daveshah1/openMixR/fpga/vivado/openmixr_base/openmixr_base.cache/ip/b018d6374f05f04f/init_config_rom_stub.v

// Copyright 1986-2016 Xilinx, Inc. All Rights Reserved.
// --------------------------------------------------------------------------------
// Tool Version: Vivado v.2016.3 (lin64) Build 1682563 Mon Oct 10 19:07:26 MDT 2016
// Date        : Thu May  4 16:19:46 2017
// Host        : david-desktop-arch running 64-bit unknown
// Command     : write_verilog -force -mode synth_stub -rename_top decalper_eb_ot_sdeen_pot_pi_dehcac_xnilix -prefix
//               decalper_eb_ot_sdeen_pot_pi_dehcac_xnilix_ init_config_rom_stub.v
// Design      : init_config_rom
// Purpose     : Stub declaration of top-level module interface
// Device      : xc7a200tfbg484-3
// --------------------------------------------------------------------------------

// This empty module with port declaration file causes synthesis tools to infer a black box for IP.
// The synthesis directives are for Synopsys Synplify support to prevent IO buffer insertion.
// Please paste the declaration into a Verilog source file or add the file as an additional source.
(* x_core_info = "blk_mem_gen_v8_3_4,Vivado 2016.3" *)
module decalper_eb_ot_sdeen_pot_pi_dehcac_xnilix(clka, addra, douta)
/* synthesis syn_black_box black_box_pad_pin="clka,addra[9:0],douta[31:0]" */;
  input clka;
  input [9:0]addra;
  output [31:0]douta;
endmodule
