daveshah1/openMixR/fpga/vivado/openmixr_base/openmixr_base.cache/ip/b018d6374f05f04f/init_config_rom_sim_netlist.v

// Copyright 1986-2016 Xilinx, Inc. All Rights Reserved.
// --------------------------------------------------------------------------------
// Tool Version: Vivado v.2016.3 (lin64) Build 1682563 Mon Oct 10 19:07:26 MDT 2016
// Date        : Thu May  4 16:19:46 2017
// Host        : david-desktop-arch running 64-bit unknown
// Command     : write_verilog -force -mode funcsim -rename_top decalper_eb_ot_sdeen_pot_pi_dehcac_xnilix -prefix
//               decalper_eb_ot_sdeen_pot_pi_dehcac_xnilix_ init_config_rom_sim_netlist.v
// Design      : init_config_rom
// Purpose     : This verilog netlist is a functional simulation representation of the design and should not be modified
//               or synthesized. This netlist cannot be used for SDF annotated simulation.
// Device      : xc7a200tfbg484-3
// --------------------------------------------------------------------------------
`timescale 1 ps / 1 ps

(* CHECK_LICENSE_TYPE = "init_config_rom,blk_mem_gen_v8_3_4,{}" *) (* downgradeipidentifiedwarnings = "yes" *) (* x_core_info = "blk_mem_gen_v8_3_4,Vivado 2016.3" *) 
(* NotValidForBitStream *)
module decalper_eb_ot_sdeen_pot_pi_dehcac_xnilix
   (clka,
    addra,
    douta);
  (* x_interface_info = "xilinx.com:interface:bram:1.0 BRAM_PORTA CLK" *) input clka;
  (* x_interface_info = "xilinx.com:interface:bram:1.0 BRAM_PORTA ADDR" *) input [9:0]addra;
  (* x_interface_info = "xilinx.com:interface:bram:1.0 BRAM_PORTA DOUT" *) output [31:0]douta;

  wire [9:0]addra;
  wire clka;
  wire [31:0]douta;
  wire NLW_U0_dbiterr_UNCONNECTED;
  wire NLW_U0_rsta_busy_UNCONNECTED;
  wire NLW_U0_rstb_busy_UNCONNECTED;
  wire NLW_U0_s_axi_arready_UNCONNECTED;
  wire NLW_U0_s_axi_awready_UNCONNECTED;
  wire NLW_U0_s_axi_bvalid_UNCONNECTED;
  wire NLW_U0_s_axi_dbiterr_UNCONNECTED;
  wire NLW_U0_s_axi_rlast_UNCONNECTED;
  wire NLW_U0_s_axi_rvalid_UNCONNECTED;
  wire NLW_U0_s_axi_sbiterr_UNCONNECTED;
  wire NLW_U0_s_axi_wready_UNCONNECTED;
  wire NLW_U0_sbiterr_UNCONNECTED;
  wire [31:0]NLW_U0_doutb_UNCONNECTED;
  wire [9:0]NLW_U0_rdaddrecc_UNCONNECTED;
  wire [3:0]NLW_U0_s_axi_bid_UNCONNECTED;
  wire [1:0]NLW_U0_s_axi_bresp_UNCONNECTED;
  wire [9:0]NLW_U0_s_axi_rdaddrecc_UNCONNECTED;
  wire [31:0]NLW_U0_s_axi_rdata_UNCONNECTED;
  wire [3:0]NLW_U0_s_axi_rid_UNCONNECTED;
  wire [1:0]NLW_U0_s_axi_rresp_UNCONNECTED;

  (* C_ADDRA_WIDTH = "10" *) 
  (* C_ADDRB_WIDTH = "10" *) 
  (* C_ALGORITHM = "1" *) 
  (* C_AXI_ID_WIDTH = "4" *) 
  (* C_AXI_SLAVE_TYPE = "0" *) 
  (* C_AXI_TYPE = "1" *) 
  (* C_BYTE_SIZE = "9" *) 
  (* C_COMMON_CLK = "0" *) 
  (* C_COUNT_18K_BRAM = "0" *) 
  (* C_COUNT_36K_BRAM = "1" *) 
  (* C_CTRL_ECC_ALGO = "NONE" *) 
  (* C_DEFAULT_DATA = "0" *) 
  (* C_DISABLE_WARN_BHV_COLL = "0" *) 
  (* C_DISABLE_WARN_BHV_RANGE = "0" *) 
  (* C_ELABORATION_DIR = "./" *) 
  (* C_ENABLE_32BIT_ADDRESS = "0" *) 
  (* C_EN_DEEPSLEEP_PIN = "0" *) 
  (* C_EN_ECC_PIPE = "0" *) 
  (* C_EN_RDADDRA_CHG = "0" *) 
  (* C_EN_RDADDRB_CHG = "0" *) 
  (* C_EN_SAFETY_CKT = "0" *) 
  (* C_EN_SHUTDOWN_PIN = "0" *) 
  (* C_EN_SLEEP_PIN = "0" *) 
  (* C_EST_POWER_SUMMARY = "Estimated Power for IP     :     2.622 mW" *) 
  (* C_FAMILY = "artix7" *) 
  (* C_HAS_AXI_ID = "0" *) 
  (* C_HAS_ENA = "0" *) 
  (* C_HAS_ENB = "0" *) 
  (* C_HAS_INJECTERR = "0" *) 
  (* C_HAS_MEM_OUTPUT_REGS_A = "0" *) 
  (* C_HAS_MEM_OUTPUT_REGS_B = "0" *) 
  (* C_HAS_MUX_OUTPUT_REGS_A = "0" *) 
  (* C_HAS_MUX_OUTPUT_REGS_B = "0" *) 
  (* C_HAS_REGCEA = "0" *) 
  (* C_HAS_REGCEB = "0" *) 
  (* C_HAS_RSTA = "0" *) 
  (* C_HAS_RSTB = "0" *) 
  (* C_HAS_SOFTECC_INPUT_REGS_A = "0" *) 
  (* C_HAS_SOFTECC_OUTPUT_REGS_B = "0" *) 
  (* C_INITA_VAL = "0" *) 
  (* C_INITB_VAL = "0" *) 
  (* C_INIT_FILE = "init_config_rom.mem" *) 
  (* C_INIT_FILE_NAME = "no_coe_file_loaded" *) 
  (* C_INTERFACE_TYPE = "0" *) 
  (* C_LOAD_INIT_FILE = "0" *) 
  (* C_MEM_TYPE = "3" *) 
  (* C_MUX_PIPELINE_STAGES = "0" *) 
  (* C_PRIM_TYPE = "1" *) 
  (* C_READ_DEPTH_A = "1024" *) 
  (* C_READ_DEPTH_B = "1024" *) 
  (* C_READ_WIDTH_A = "32" *) 
  (* C_READ_WIDTH_B = "32" *) 
  (* C_RSTRAM_A = "0" *) 
  (* C_RSTRAM_B = "0" *) 
  (* C_RST_PRIORITY_A = "CE" *) 
  (* C_RST_PRIORITY_B = "CE" *) 
  (* C_SIM_COLLISION_CHECK = "ALL" *) 
  (* C_USE_BRAM_BLOCK = "0" *) 
  (* C_USE_BYTE_WEA = "0" *) 
  (* C_USE_BYTE_WEB = "0" *) 
  (* C_USE_DEFAULT_DATA = "0" *) 
  (* C_USE_ECC = "0" *) 
  (* C_USE_SOFTECC = "0" *) 
  (* C_USE_URAM = "0" *) 
  (* C_WEA_WIDTH = "1" *) 
  (* C_WEB_WIDTH = "1" *) 
  (* C_WRITE_DEPTH_A = "1024" *) 
  (* C_WRITE_DEPTH_B = "1024" *) 
  (* C_WRITE_MODE_A = "WRITE_FIRST" *) 
  (* C_WRITE_MODE_B = "WRITE_FIRST" *) 
  (* C_WRITE_WIDTH_A = "32" *) 
  (* C_WRITE_WIDTH_B = "32" *) 
  (* C_XDEVICEFAMILY = "artix7" *) 
  (* downgradeipidentifiedwarnings = "yes" *) 
  decalper_eb_ot_sdeen_pot_pi_dehcac_xnilix_blk_mem_gen_v8_3_4 U0
       (.addra(addra),
        .addrb({1'b0,1'b0,1'b0,1'b0,1'b0,1'b0,1'b0,1'b0,1'b0,1'b0}),
        .clka(clka),
        .clkb(1'b0),
        .dbiterr(NLW_U0_dbiterr_UNCONNECTED),
        .deepsleep(1'b0),
        .dina({1'b0,1'b0,1'b0,1'b0,1'b0,1'b0,1'b0,1'b0,1'b0,1'b0,1'b0,1'b0,1'b0,1'b0,1'b0,1'b0,1'b0,1'b0,1'b0,1'b0,1'b0,1'b0,1'b0,1'b0,1'b0,1'b0,1'b0,1'b0,1'b0,1'b0,1'b0,1'b0}),
        .dinb({1'b0,1'b0,1'b0,1'b0,1'b0,1'b0,1'b0,1'b0,1'b0,1'b0,1'b0,1'b0,1'b0,1'b0,1'b0,1'b0,1'b0,1'b0,1'b0,1'b0,1'b0,1'b0,1'b0,1'b0,1'b0,1'b0,1'b0,1'b0,1'b0,1'b0,1'b0,1'b0}),
        .douta(douta),
        .doutb(NLW_U0_doutb_UNCONNECTED[31:0]),
        .eccpipece(1'b0),
        .ena(1'b0),
        .enb(1'b0),
        .injectdbiterr(1'b0),
        .injectsbiterr(1'b0),
        .rdaddrecc(NLW_U0_rdaddrecc_UNCONNECTED[9:0]),
        .regcea(1'b0),
        .regceb(1'b0),
        .rsta(1'b0),
        .rsta_busy(NLW_U0_rsta_busy_UNCONNECTED),
        .rstb(1'b0),
        .rstb_busy(NLW_U0_rstb_busy_UNCONNECTED),
        .s_aclk(1'b0),
        .s_aresetn(1'b0),
        .s_axi_araddr({1'b0,1'b0,1'b0,1'b0,1'b0,1'b0,1'b0,1'b0,1'b0,1'b0,1'b0,1'b0,1'b0,1'b0,1'b0,1'b0,1'b0,1'b0,1'b0,1'b0,1'b0,1'b0,1'b0,1'b0,1'b0,1'b0,1'b0,1'b0,1'b0,1'b0,1'b0,1'b0}),
        .s_axi_arburst({1'b0,1'b0}),
        .s_axi_arid({1'b0,1'b0,1'b0,1'b0}),
        .s_axi_arlen({1'b0,1'b0,1'b0,1'b0,1'b0,1'b0,1'b0,1'b0}),
        .s_axi_arready(NLW_U0_s_axi_arready_UNCONNECTED),
        .s_axi_arsize({1'b0,1'b0,1'b0}),
        .s_axi_arvalid(1'b0),
        .s_axi_awaddr({1'b0,1'b0,1'b0,1'b0,1'b0,1'b0,1'b0,1'b0,1'b0,1'b0,1'b0,1'b0,1'b0,1'b0,1'b0,1'b0,1'b0,1'b0,1'b0,1'b0,1'b0,1'b0,1'b0,1'b0,1'b0,1'b0,1'b0,1'b0,1'b0,1'b0,1'b0,1'b0}),
        .s_axi_awburst({1'b0,1'b0}),
        .s_axi_awid({1'b0,1'b0,1'b0,1'b0}),
        .s_axi_awlen({1'b0,1'b0,1'b0,1'b0,1'b0,1'b0,1'b0,1'b0}),
        .s_axi_awready(NLW_U0_s_axi_awready_UNCONNECTED),
        .s_axi_awsize({1'b0,1'b0,1'b0}),
        .s_axi_awvalid(1'b0),
        .s_axi_bid(NLW_U0_s_axi_bid_UNCONNECTED[3:0]),
        .s_axi_bready(1'b0),
        .s_axi_bresp(NLW_U0_s_axi_bresp_UNCONNECTED[1:0]),
        .s_axi_bvalid(NLW_U0_s_axi_bvalid_UNCONNECTED),
        .s_axi_dbiterr(NLW_U0_s_axi_dbiterr_UNCONNECTED),
        .s_axi_injectdbiterr(1'b0),
        .s_axi_injectsbiterr(1'b0),
        .s_axi_rdaddrecc(NLW_U0_s_axi_rdaddrecc_UNCONNECTED[9:0]),
        .s_axi_rdata(NLW_U0_s_axi_rdata_UNCONNECTED[31:0]),
        .s_axi_rid(NLW_U0_s_axi_rid_UNCONNECTED[3:0]),
        .s_axi_rlast(NLW_U0_s_axi_rlast_UNCONNECTED),
        .s_axi_rready(1'b0),
        .s_axi_rresp(NLW_U0_s_axi_rresp_UNCONNECTED[1:0]),
        .s_axi_rvalid(NLW_U0_s_axi_rvalid_UNCONNECTED),
        .s_axi_sbiterr(NLW_U0_s_axi_sbiterr_UNCONNECTED),
        .s_axi_wdata({1'b0,1'b0,1'b0,1'b0,1'b0,1'b0,1'b0,1'b0,1'b0,1'b0,1'b0,1'b0,1'b0,1'b0,1'b0,1'b0,1'b0,1'b0,1'b0,1'b0,1'b0,1'b0,1'b0,1'b0,1'b0,1'b0,1'b0,1'b0,1'b0,1'b0,1'b0,1'b0}),
        .s_axi_wlast(1'b0),
        .s_axi_wready(NLW_U0_s_axi_wready_UNCONNECTED),
        .s_axi_wstrb(1'b0),
        .s_axi_wvalid(1'b0),
        .sbiterr(NLW_U0_sbiterr_UNCONNECTED),
        .shutdown(1'b0),
        .sleep(1'b0),
        .wea(1'b0),
        .web(1'b0));
endmodule

module decalper_eb_ot_sdeen_pot_pi_dehcac_xnilix_blk_mem_gen_generic_cstr
   (douta,
    clka,
    addra);
  output [31:0]douta;
  input clka;
  input [9:0]addra;

  wire [9:0]addra;
  wire clka;
  wire [31:0]douta;

  decalper_eb_ot_sdeen_pot_pi_dehcac_xnilix_blk_mem_gen_prim_width \ramloop[0].ram.r 
       (.addra(addra),
        .clka(clka),
        .douta(douta));
endmodule

module decalper_eb_ot_sdeen_pot_pi_dehcac_xnilix_blk_mem_gen_prim_width
   (douta,
    clka,
    addra);
  output [31:0]douta;
  input clka;
  input [9:0]addra;

  wire [9:0]addra;
  wire clka;
  wire [31:0]douta;

  decalper_eb_ot_sdeen_pot_pi_dehcac_xnilix_blk_mem_gen_prim_wrapper \prim_noinit.ram 
       (.addra(addra),
        .clka(clka),
        .douta(douta));
endmodule

module decalper_eb_ot_sdeen_pot_pi_dehcac_xnilix_blk_mem_gen_prim_wrapper
   (douta,
    clka,
    addra);
  output [31:0]douta;
  input clka;
  input [9:0]addra;

  wire \DEVICE_7SERIES.NO_BMM_INFO.SP.SIMPLE_PRIM36.ram_n_85 ;
  wire \DEVICE_7SERIES.NO_BMM_INFO.SP.SIMPLE_PRIM36.ram_n_86 ;
  wire \DEVICE_7SERIES.NO_BMM_INFO.SP.SIMPLE_PRIM36.ram_n_87 ;
  wire \DEVICE_7SERIES.NO_BMM_INFO.SP.SIMPLE_PRIM36.ram_n_88 ;
  wire [9:0]addra;
  wire clka;
  wire [31:0]douta;
  wire \NLW_DEVICE_7SERIES.NO_BMM_INFO.SP.SIMPLE_PRIM36.ram_CASCADEOUTA_UNCONNECTED ;
  wire \NLW_DEVICE_7SERIES.NO_BMM_INFO.SP.SIMPLE_PRIM36.ram_CASCADEOUTB_UNCONNECTED ;
  wire \NLW_DEVICE_7SERIES.NO_BMM_INFO.SP.SIMPLE_PRIM36.ram_DBITERR_UNCONNECTED ;
  wire \NLW_DEVICE_7SERIES.NO_BMM_INFO.SP.SIMPLE_PRIM36.ram_SBITERR_UNCONNECTED ;
  wire [31:0]\NLW_DEVICE_7SERIES.NO_BMM_INFO.SP.SIMPLE_PRIM36.ram_DOBDO_UNCONNECTED ;
  wire [3:0]\NLW_DEVICE_7SERIES.NO_BMM_INFO.SP.SIMPLE_PRIM36.ram_DOPBDOP_UNCONNECTED ;
  wire [7:0]\NLW_DEVICE_7SERIES.NO_BMM_INFO.SP.SIMPLE_PRIM36.ram_ECCPARITY_UNCONNECTED ;
  wire [8:0]\NLW_DEVICE_7SERIES.NO_BMM_INFO.SP.SIMPLE_PRIM36.ram_RDADDRECC_UNCONNECTED ;

  (* CLOCK_DOMAINS = "COMMON" *) 
  (* box_type = "PRIMITIVE" *) 
  RAMB36E1 #(
    .DOA_REG(0),
    .DOB_REG(0),
    .EN_ECC_READ("FALSE"),
    .EN_ECC_WRITE("FALSE"),
    .INITP_00(256'h0000000000000000000000000000000000000000000000000000000000000000),
    .INITP_01(256'h0000000000000000000000000000000000000000000000000000000000000000),
    .INITP_02(256'h0000000000000000000000000000000000000000000000000000000000000000),
    .INITP_03(256'h0000000000000000000000000000000000000000000000000000000000000000),
    .INITP_04(256'h0000000000000000000000000000000000000000000000000000000000000000),
    .INITP_05(256'h0000000000000000000000000000000000000000000000000000000000000000),
    .INITP_06(256'h0000000000000000000000000000000000000000000000000000000000000000),
    .INITP_07(256'h0000000000000000000000000000000000000000000000000000000000000000),
    .INITP_08(256'h0000000000000000000000000000000000000000000000000000000000000000),
    .INITP_09(256'h0000000000000000000000000000000000000000000000000000000000000000),
    .INITP_0A(256'h0000000000000000000000000000000000000000000000000000000000000000),
    .INITP_0B(256'h0000000000000000000000000000000000000000000000000000000000000000),
    .INITP_0C(256'h0000000000000000000000000000000000000000000000000000000000000000),
    .INITP_0D(256'h0000000000000000000000000000000000000000000000000000000000000000),
    .INITP_0E(256'h0000000000000000000000000000000000000000000000000000000000000000),
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
    .INIT_77(256'h0000000000000000000000000000000000000000000000000000000000000000),
    .INIT_78(256'h0000000000000000000000000000000000000000000000000000000000000000),
    .INIT_79(256'h0000000000000000000000000000000000000000000000000000000000000000),
    .INIT_7A(256'h0000000000000000000000000000000000000000000000000000000000000000),
    .INIT_7B(256'h0000000000000000000000000000000000000000000000000000000000000000),
    .INIT_7C(256'h0000000000000000000000000000000000000000000000000000000000000000),
    .INIT_7D(256'h0000000000000000000000000000000000000000000000000000000000000000),
    .INIT_7E(256'h0000000000000000000000000000000000000000000000000000000000000000),
    .INIT_7F(256'h0000000000000000000000000000000000000000000000000000000000000000),
    .INIT_A(36'h000000000),
    .INIT_B(36'h000000000),
    .INIT_FILE("NONE"),
    .IS_CLKARDCLK_INVERTED(1'b0),
    .IS_CLKBWRCLK_INVERTED(1'b0),
    .IS_ENARDEN_INVERTED(1'b0),
    .IS_ENBWREN_INVERTED(1'b0),
    .IS_RSTRAMARSTRAM_INVERTED(1'b0),
    .IS_RSTRAMB_INVERTED(1'b0),
    .IS_RSTREGARSTREG_INVERTED(1'b0),
    .IS_RSTREGB_INVERTED(1'b0),
    .RAM_EXTENSION_A("NONE"),
    .RAM_EXTENSION_B("NONE"),
    .RAM_MODE("TDP"),
    .RDADDR_COLLISION_HWCONFIG("PERFORMANCE"),
    .READ_WIDTH_A(36),
    .READ_WIDTH_B(36),
    .RSTREG_PRIORITY_A("REGCE"),
    .RSTREG_PRIORITY_B("REGCE"),
    .SIM_COLLISION_CHECK("ALL"),
    .SIM_DEVICE("7SERIES"),
    .SRVAL_A(36'h000000000),
    .SRVAL_B(36'h000000000),
    .WRITE_MODE_A("WRITE_FIRST"),
    .WRITE_MODE_B("WRITE_FIRST"),
    .WRITE_WIDTH_A(36),
    .WRITE_WIDTH_B(36)) 
    \DEVICE_7SERIES.NO_BMM_INFO.SP.SIMPLE_PRIM36.ram 
       (.ADDRARDADDR({1'b1,addra,1'b1,1'b1,1'b1,1'b1,1'b1}),
        .ADDRBWRADDR({1'b0,1'b0,1'b0,1'b0,1'b0,1'b0,1'b0,1'b0,1'b0,1'b0,1'b0,1'b0,1'b0,1'b0,1'b0,1'b0}),
        .CASCADEINA(1'b0),
        .CASCADEINB(1'b0),
        .CASCADEOUTA(\NLW_DEVICE_7SERIES.NO_BMM_INFO.SP.SIMPLE_PRIM36.ram_CASCADEOUTA_UNCONNECTED ),
        .CASCADEOUTB(\NLW_DEVICE_7SERIES.NO_BMM_INFO.SP.SIMPLE_PRIM36.ram_CASCADEOUTB_UNCONNECTED ),
        .CLKARDCLK(clka),
        .CLKBWRCLK(clka),
        .DBITERR(\NLW_DEVICE_7SERIES.NO_BMM_INFO.SP.SIMPLE_PRIM36.ram_DBITERR_UNCONNECTED ),
        .DIADI({1'b0,1'b0,1'b0,1'b0,1'b0,1'b0,1'b0,1'b0,1'b0,1'b0,1'b0,1'b0,1'b0,1'b0,1'b0,1'b0,1'b0,1'b0,1'b0,1'b0,1'b0,1'b0,1'b0,1'b0,1'b0,1'b0,1'b0,1'b0,1'b0,1'b0,1'b0,1'b0}),
        .DIBDI({1'b0,1'b0,1'b0,1'b0,1'b0,1'b0,1'b0,1'b0,1'b0,1'b0,1'b0,1'b0,1'b0,1'b0,1'b0,1'b0,1'b0,1'b0,1'b0,1'b0,1'b0,1'b0,1'b0,1'b0,1'b0,1'b0,1'b0,1'b0,1'b0,1'b0,1'b0,1'b0}),
        .DIPADIP({1'b0,1'b0,1'b0,1'b0}),
        .DIPBDIP({1'b0,1'b0,1'b0,1'b0}),
        .DOADO(douta),
        .DOBDO(\NLW_DEVICE_7SERIES.NO_BMM_INFO.SP.SIMPLE_PRIM36.ram_DOBDO_UNCONNECTED [31:0]),
        .DOPADOP({\DEVICE_7SERIES.NO_BMM_INFO.SP.SIMPLE_PRIM36.ram_n_85 ,\DEVICE_7SERIES.NO_BMM_INFO.SP.SIMPLE_PRIM36.ram_n_86 ,\DEVICE_7SERIES.NO_BMM_INFO.SP.SIMPLE_PRIM36.ram_n_87 ,\DEVICE_7SERIES.NO_BMM_INFO.SP.SIMPLE_PRIM36.ram_n_88 }),
        .DOPBDOP(\NLW_DEVICE_7SERIES.NO_BMM_INFO.SP.SIMPLE_PRIM36.ram_DOPBDOP_UNCONNECTED [3:0]),
        .ECCPARITY(\NLW_DEVICE_7SERIES.NO_BMM_INFO.SP.SIMPLE_PRIM36.ram_ECCPARITY_UNCONNECTED [7:0]),
        .ENARDEN(1'b1),
        .ENBWREN(1'b0),
        .INJECTDBITERR(1'b0),
        .INJECTSBITERR(1'b0),
        .RDADDRECC(\NLW_DEVICE_7SERIES.NO_BMM_INFO.SP.SIMPLE_PRIM36.ram_RDADDRECC_UNCONNECTED [8:0]),
        .REGCEAREGCE(1'b0),
        .REGCEB(1'b0),
        .RSTRAMARSTRAM(1'b0),
        .RSTRAMB(1'b0),
        .RSTREGARSTREG(1'b0),
        .RSTREGB(1'b0),
        .SBITERR(\NLW_DEVICE_7SERIES.NO_BMM_INFO.SP.SIMPLE_PRIM36.ram_SBITERR_UNCONNECTED ),
        .WEA({1'b0,1'b0,1'b0,1'b0}),
        .WEBWE({1'b0,1'b0,1'b0,1'b0,1'b0,1'b0,1'b0,1'b0}));
endmodule

module decalper_eb_ot_sdeen_pot_pi_dehcac_xnilix_blk_mem_gen_top
   (douta,
    clka,
    addra);
  output [31:0]douta;
  input clka;
  input [9:0]addra;

  wire [9:0]addra;
  wire clka;
  wire [31:0]douta;

  decalper_eb_ot_sdeen_pot_pi_dehcac_xnilix_blk_mem_gen_generic_cstr \valid.cstr 
       (.addra(addra),
        .clka(clka),
        .douta(douta));
endmodule

(* C_ADDRA_WIDTH = "10" *) (* C_ADDRB_WIDTH = "10" *) (* C_ALGORITHM = "1" *) 
(* C_AXI_ID_WIDTH = "4" *) (* C_AXI_SLAVE_TYPE = "0" *) (* C_AXI_TYPE = "1" *) 
(* C_BYTE_SIZE = "9" *) (* C_COMMON_CLK = "0" *) (* C_COUNT_18K_BRAM = "0" *) 
(* C_COUNT_36K_BRAM = "1" *) (* C_CTRL_ECC_ALGO = "NONE" *) (* C_DEFAULT_DATA = "0" *) 
(* C_DISABLE_WARN_BHV_COLL = "0" *) (* C_DISABLE_WARN_BHV_RANGE = "0" *) (* C_ELABORATION_DIR = "./" *) 
(* C_ENABLE_32BIT_ADDRESS = "0" *) (* C_EN_DEEPSLEEP_PIN = "0" *) (* C_EN_ECC_PIPE = "0" *) 
(* C_EN_RDADDRA_CHG = "0" *) (* C_EN_RDADDRB_CHG = "0" *) (* C_EN_SAFETY_CKT = "0" *) 
(* C_EN_SHUTDOWN_PIN = "0" *) (* C_EN_SLEEP_PIN = "0" *) (* C_EST_POWER_SUMMARY = "Estimated Power for IP     :     2.622 mW" *) 
(* C_FAMILY = "artix7" *) (* C_HAS_AXI_ID = "0" *) (* C_HAS_ENA = "0" *) 
(* C_HAS_ENB = "0" *) (* C_HAS_INJECTERR = "0" *) (* C_HAS_MEM_OUTPUT_REGS_A = "0" *) 
(* C_HAS_MEM_OUTPUT_REGS_B = "0" *) (* C_HAS_MUX_OUTPUT_REGS_A = "0" *) (* C_HAS_MUX_OUTPUT_REGS_B = "0" *) 
(* C_HAS_REGCEA = "0" *) (* C_HAS_REGCEB = "0" *) (* C_HAS_RSTA = "0" *) 
(* C_HAS_RSTB = "0" *) (* C_HAS_SOFTECC_INPUT_REGS_A = "0" *) (* C_HAS_SOFTECC_OUTPUT_REGS_B = "0" *) 
(* C_INITA_VAL = "0" *) (* C_INITB_VAL = "0" *) (* C_INIT_FILE = "init_config_rom.mem" *) 
(* C_INIT_FILE_NAME = "no_coe_file_loaded" *) (* C_INTERFACE_TYPE = "0" *) (* C_LOAD_INIT_FILE = "0" *) 
(* C_MEM_TYPE = "3" *) (* C_MUX_PIPELINE_STAGES = "0" *) (* C_PRIM_TYPE = "1" *) 
(* C_READ_DEPTH_A = "1024" *) (* C_READ_DEPTH_B = "1024" *) (* C_READ_WIDTH_A = "32" *) 
(* C_READ_WIDTH_B = "32" *) (* C_RSTRAM_A = "0" *) (* C_RSTRAM_B = "0" *) 
(* C_RST_PRIORITY_A = "CE" *) (* C_RST_PRIORITY_B = "CE" *) (* C_SIM_COLLISION_CHECK = "ALL" *) 
(* C_USE_BRAM_BLOCK = "0" *) (* C_USE_BYTE_WEA = "0" *) (* C_USE_BYTE_WEB = "0" *) 
(* C_USE_DEFAULT_DATA = "0" *) (* C_USE_ECC = "0" *) (* C_USE_SOFTECC = "0" *) 
(* C_USE_URAM = "0" *) (* C_WEA_WIDTH = "1" *) (* C_WEB_WIDTH = "1" *) 
(* C_WRITE_DEPTH_A = "1024" *) (* C_WRITE_DEPTH_B = "1024" *) (* C_WRITE_MODE_A = "WRITE_FIRST" *) 
(* C_WRITE_MODE_B = "WRITE_FIRST" *) (* C_WRITE_WIDTH_A = "32" *) (* C_WRITE_WIDTH_B = "32" *) 
(* C_XDEVICEFAMILY = "artix7" *) (* downgradeipidentifiedwarnings = "yes" *) 
module decalper_eb_ot_sdeen_pot_pi_dehcac_xnilix_blk_mem_gen_v8_3_4
   (clka,
    rsta,
    ena,
    regcea,
    wea,
    addra,
    dina,
    douta,
    clkb,
    rstb,
    enb,
    regceb,
    web,
    addrb,
    dinb,
    doutb,
    injectsbiterr,
    injectdbiterr,
    eccpipece,
    sbiterr,
    dbiterr,
    rdaddrecc,
    sleep,
    deepsleep,
    shutdown,
    rsta_busy,
    rstb_busy,
    s_aclk,
    s_aresetn,
    s_axi_awid,
    s_axi_awaddr,
    s_axi_awlen,
    s_axi_awsize,
    s_axi_awburst,
    s_axi_awvalid,
    s_axi_awready,
    s_axi_wdata,
    s_axi_wstrb,
    s_axi_wlast,
    s_axi_wvalid,
    s_axi_wready,
    s_axi_bid,
    s_axi_bresp,
    s_axi_bvalid,
    s_axi_bready,
    s_axi_arid,
    s_axi_araddr,
    s_axi_arlen,
    s_axi_arsize,
    s_axi_arburst,
    s_axi_arvalid,
    s_axi_arready,
    s_axi_rid,
    s_axi_rdata,
    s_axi_rresp,
    s_axi_rlast,
    s_axi_rvalid,
    s_axi_rready,
    s_axi_injectsbiterr,
    s_axi_injectdbiterr,
    s_axi_sbiterr,
    s_axi_dbiterr,
    s_axi_rdaddrecc);
  input clka;
  input rsta;
  input ena;
  input regcea;
  input [0:0]wea;
  input [9:0]addra;
  input [31:0]dina;
  output [31:0]douta;
  input clkb;
  input rstb;
  input enb;
  input regceb;
  input [0:0]web;
  input [9:0]addrb;
  input [31:0]dinb;
  output [31:0]doutb;
  input injectsbiterr;
  input injectdbiterr;
  input eccpipece;
  output sbiterr;
  output dbiterr;
  output [9:0]rdaddrecc;
  input sleep;
  input deepsleep;
  input shutdown;
  output rsta_busy;
  output rstb_busy;
  input s_aclk;
  input s_aresetn;
  input [3:0]s_axi_awid;
  input [31:0]s_axi_awaddr;
  input [7:0]s_axi_awlen;
  input [2:0]s_axi_awsize;
  input [1:0]s_axi_awburst;
  input s_axi_awvalid;
  output s_axi_awready;
  input [31:0]s_axi_wdata;
  input [0:0]s_axi_wstrb;
  input s_axi_wlast;
  input s_axi_wvalid;
  output s_axi_wready;
  output [3:0]s_axi_bid;
  output [1:0]s_axi_bresp;
  output s_axi_bvalid;
  input s_axi_bready;
  input [3:0]s_axi_arid;
  input [31:0]s_axi_araddr;
  input [7:0]s_axi_arlen;
  input [2:0]s_axi_arsize;
  input [1:0]s_axi_arburst;
  input s_axi_arvalid;
  output s_axi_arready;
  output [3:0]s_axi_rid;
  output [31:0]s_axi_rdata;
  output [1:0]s_axi_rresp;
  output s_axi_rlast;
  output s_axi_rvalid;
  input s_axi_rready;
  input s_axi_injectsbiterr;
  input s_axi_injectdbiterr;
  output s_axi_sbiterr;
  output s_axi_dbiterr;
  output [9:0]s_axi_rdaddrecc;

  wire \<const0> ;
  wire [9:0]addra;
  wire clka;
  wire [31:0]douta;

  assign dbiterr = \<const0> ;
  assign doutb[31] = \<const0> ;
  assign doutb[30] = \<const0> ;
  assign doutb[29] = \<const0> ;
  assign doutb[28] = \<const0> ;
  assign doutb[27] = \<const0> ;
  assign doutb[26] = \<const0> ;
  assign doutb[25] = \<const0> ;
  assign doutb[24] = \<const0> ;
  assign doutb[23] = \<const0> ;
  assign doutb[22] = \<const0> ;
  assign doutb[21] = \<const0> ;
  assign doutb[20] = \<const0> ;
  assign doutb[19] = \<const0> ;
  assign doutb[18] = \<const0> ;
  assign doutb[17] = \<const0> ;
  assign doutb[16] = \<const0> ;
  assign doutb[15] = \<const0> ;
  assign doutb[14] = \<const0> ;
  assign doutb[13] = \<const0> ;
  assign doutb[12] = \<const0> ;
  assign doutb[11] = \<const0> ;
  assign doutb[10] = \<const0> ;
  assign doutb[9] = \<const0> ;
  assign doutb[8] = \<const0> ;
  assign doutb[7] = \<const0> ;
  assign doutb[6] = \<const0> ;
  assign doutb[5] = \<const0> ;
  assign doutb[4] = \<const0> ;
  assign doutb[3] = \<const0> ;
  assign doutb[2] = \<const0> ;
  assign doutb[1] = \<const0> ;
  assign doutb[0] = \<const0> ;
  assign rdaddrecc[9] = \<const0> ;
  assign rdaddrecc[8] = \<const0> ;
  assign rdaddrecc[7] = \<const0> ;
  assign rdaddrecc[6] = \<const0> ;
  assign rdaddrecc[5] = \<const0> ;
  assign rdaddrecc[4] = \<const0> ;
  assign rdaddrecc[3] = \<const0> ;
  assign rdaddrecc[2] = \<const0> ;
  assign rdaddrecc[1] = \<const0> ;
  assign rdaddrecc[0] = \<const0> ;
  assign rsta_busy = \<const0> ;
  assign rstb_busy = \<const0> ;
  assign s_axi_arready = \<const0> ;
  assign s_axi_awready = \<const0> ;
  assign s_axi_bid[3] = \<const0> ;
  assign s_axi_bid[2] = \<const0> ;
  assign s_axi_bid[1] = \<const0> ;
  assign s_axi_bid[0] = \<const0> ;
  assign s_axi_bresp[1] = \<const0> ;
  assign s_axi_bresp[0] = \<const0> ;
  assign s_axi_bvalid = \<const0> ;
  assign s_axi_dbiterr = \<const0> ;
  assign s_axi_rdaddrecc[9] = \<const0> ;
  assign s_axi_rdaddrecc[8] = \<const0> ;
  assign s_axi_rdaddrecc[7] = \<const0> ;
  assign s_axi_rdaddrecc[6] = \<const0> ;
  assign s_axi_rdaddrecc[5] = \<const0> ;
  assign s_axi_rdaddrecc[4] = \<const0> ;
  assign s_axi_rdaddrecc[3] = \<const0> ;
  assign s_axi_rdaddrecc[2] = \<const0> ;
  assign s_axi_rdaddrecc[1] = \<const0> ;
  assign s_axi_rdaddrecc[0] = \<const0> ;
  assign s_axi_rdata[31] = \<const0> ;
  assign s_axi_rdata[30] = \<const0> ;
  assign s_axi_rdata[29] = \<const0> ;
  assign s_axi_rdata[28] = \<const0> ;
  assign s_axi_rdata[27] = \<const0> ;
  assign s_axi_rdata[26] = \<const0> ;
  assign s_axi_rdata[25] = \<const0> ;
  assign s_axi_rdata[24] = \<const0> ;
  assign s_axi_rdata[23] = \<const0> ;
  assign s_axi_rdata[22] = \<const0> ;
  assign s_axi_rdata[21] = \<const0> ;
  assign s_axi_rdata[20] = \<const0> ;
  assign s_axi_rdata[19] = \<const0> ;
  assign s_axi_rdata[18] = \<const0> ;
  assign s_axi_rdata[17] = \<const0> ;
  assign s_axi_rdata[16] = \<const0> ;
  assign s_axi_rdata[15] = \<const0> ;
  assign s_axi_rdata[14] = \<const0> ;
  assign s_axi_rdata[13] = \<const0> ;
  assign s_axi_rdata[12] = \<const0> ;
  assign s_axi_rdata[11] = \<const0> ;
  assign s_axi_rdata[10] = \<const0> ;
  assign s_axi_rdata[9] = \<const0> ;
  assign s_axi_rdata[8] = \<const0> ;
  assign s_axi_rdata[7] = \<const0> ;
  assign s_axi_rdata[6] = \<const0> ;
  assign s_axi_rdata[5] = \<const0> ;
  assign s_axi_rdata[4] = \<const0> ;
  assign s_axi_rdata[3] = \<const0> ;
  assign s_axi_rdata[2] = \<const0> ;
  assign s_axi_rdata[1] = \<const0> ;
  assign s_axi_rdata[0] = \<const0> ;
  assign s_axi_rid[3] = \<const0> ;
  assign s_axi_rid[2] = \<const0> ;
  assign s_axi_rid[1] = \<const0> ;
  assign s_axi_rid[0] = \<const0> ;
  assign s_axi_rlast = \<const0> ;
  assign s_axi_rresp[1] = \<const0> ;
  assign s_axi_rresp[0] = \<const0> ;
  assign s_axi_rvalid = \<const0> ;
  assign s_axi_sbiterr = \<const0> ;
  assign s_axi_wready = \<const0> ;
  assign sbiterr = \<const0> ;
  GND GND
       (.G(\<const0> ));
  decalper_eb_ot_sdeen_pot_pi_dehcac_xnilix_blk_mem_gen_v8_3_4_synth inst_blk_mem_gen
       (.addra(addra),
        .clka(clka),
        .douta(douta));
endmodule

module decalper_eb_ot_sdeen_pot_pi_dehcac_xnilix_blk_mem_gen_v8_3_4_synth
   (douta,
    clka,
    addra);
  output [31:0]douta;
  input clka;
  input [9:0]addra;

  wire [9:0]addra;
  wire clka;
  wire [31:0]douta;

  decalper_eb_ot_sdeen_pot_pi_dehcac_xnilix_blk_mem_gen_top \gnbram.gnativebmg.native_blk_mem_gen 
       (.addra(addra),
        .clka(clka),
        .douta(douta));
endmodule
`ifndef GLBL
`define GLBL
`timescale  1 ps / 1 ps

module glbl ();

    parameter ROC_WIDTH = 100000;
    parameter TOC_WIDTH = 0;

//--------   STARTUP Globals --------------
    wire GSR;
    wire GTS;
    wire GWE;
    wire PRLD;
    tri1 p_up_tmp;
    tri (weak1, strong0) PLL_LOCKG = p_up_tmp;

    wire PROGB_GLBL;
    wire CCLKO_GLBL;
    wire FCSBO_GLBL;
    wire [3:0] DO_GLBL;
    wire [3:0] DI_GLBL;
   
    reg GSR_int;
    reg GTS_int;
    reg PRLD_int;

//--------   JTAG Globals --------------
    wire JTAG_TDO_GLBL;
    wire JTAG_TCK_GLBL;
    wire JTAG_TDI_GLBL;
    wire JTAG_TMS_GLBL;
    wire JTAG_TRST_GLBL;

    reg JTAG_CAPTURE_GLBL;
    reg JTAG_RESET_GLBL;
    reg JTAG_SHIFT_GLBL;
    reg JTAG_UPDATE_GLBL;
    reg JTAG_RUNTEST_GLBL;

    reg JTAG_SEL1_GLBL = 0;
    reg JTAG_SEL2_GLBL = 0 ;
    reg JTAG_SEL3_GLBL = 0;
    reg JTAG_SEL4_GLBL = 0;

    reg JTAG_USER_TDO1_GLBL = 1'bz;
    reg JTAG_USER_TDO2_GLBL = 1'bz;
    reg JTAG_USER_TDO3_GLBL = 1'bz;
    reg JTAG_USER_TDO4_GLBL = 1'bz;

    assign (weak1, weak0) GSR = GSR_int;
    assign (weak1, weak0) GTS = GTS_int;
    assign (weak1, weak0) PRLD = PRLD_int;

    initial begin
	GSR_int = 1'b1;
	PRLD_int = 1'b1;
	#(ROC_WIDTH)
	GSR_int = 1'b0;
	PRLD_int = 1'b0;
    end

    initial begin
	GTS_int = 1'b1;
	#(TOC_WIDTH)
	GTS_int = 1'b0;
    end

endmodule
`endif
